Jasdoge/DogeTipjar/TipJar/Data/doge_received.bmp

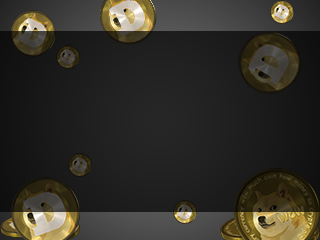
TipJar/Data/doge_received.bmp
