Jasdoge/DogeTipjar/TipJar/Data/wallpaper.bmp

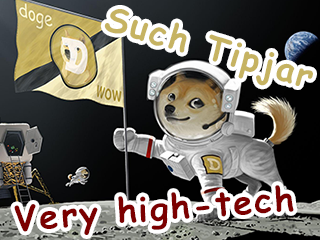
TipJar/Data/wallpaper.bmp
